sparkfun/SparkFun_GNSS_Flex_pHAT/docs/assets/3d_model/poster.png

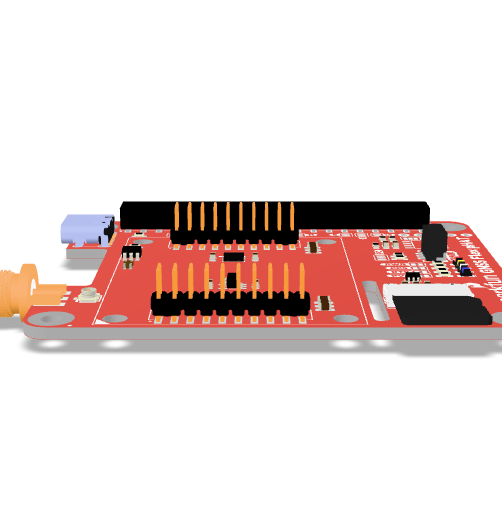
docs/assets/3d_model/poster.png
