sparkfun/SparkFun_GNSS_Flex_pHAT/Hardware/Dimensions.png

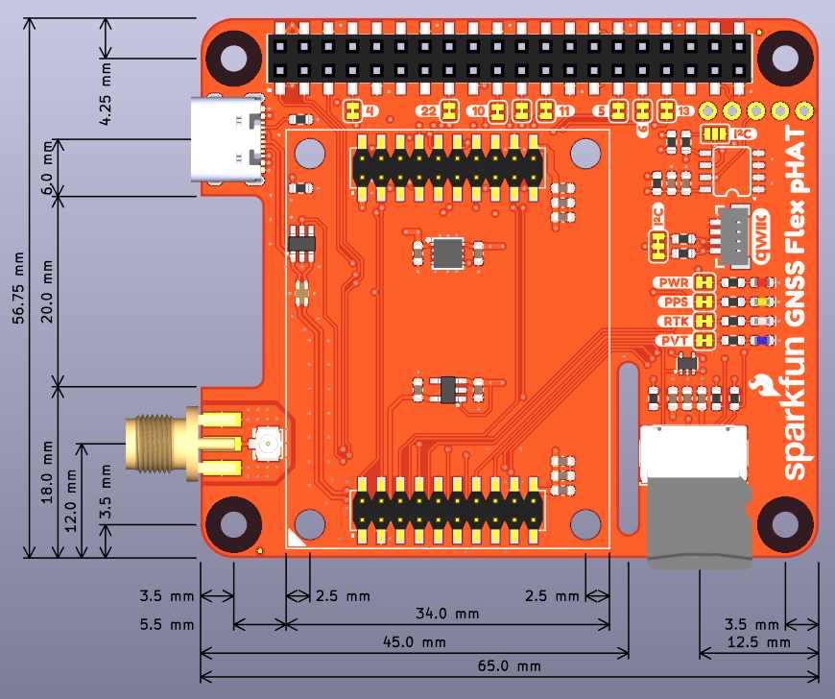
Hardware/Dimensions.png
