sparkfun/SparkFun_GNSS_Flex_pHAT/docs/assets/img/hookup_guide/assembly-raspberry_pi.jpg

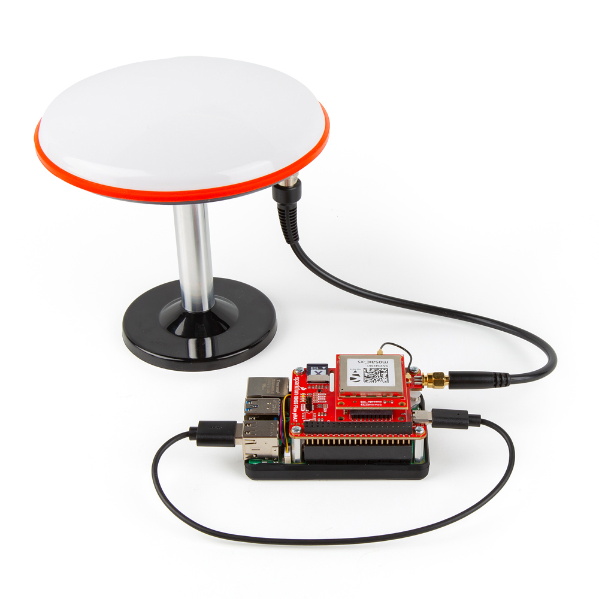
docs/assets/img/hookup_guide/assembly-raspberry_pi.jpg
